vardelean/Hex-Preamp/GI13_Hex_Preamp/3D/GI13_RevA.jpg

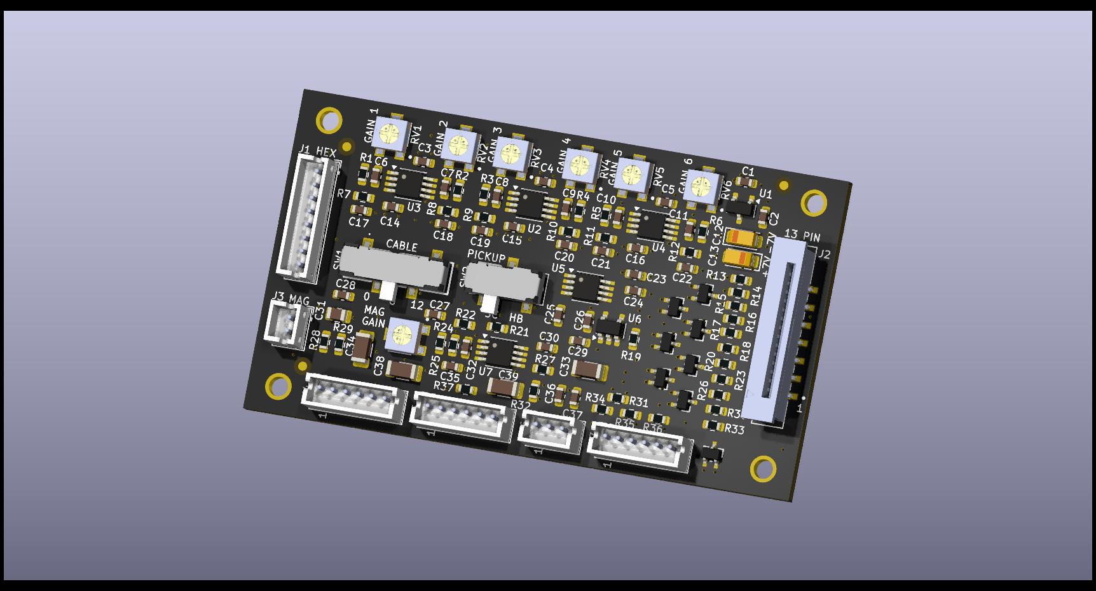
GI13_Hex_Preamp/3D/GI13_RevA.jpg
