vardelean/Hex-Preamp/Pics/GK_3_Finished_2.jpg

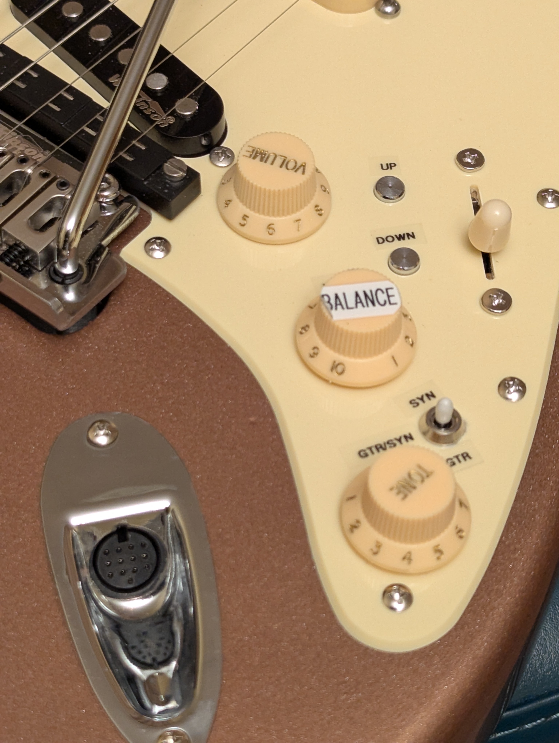
Pics/GK_3_Finished_2.jpg
