vardelean/Hex-Preamp/Pics/Hex_Preamp.jpg

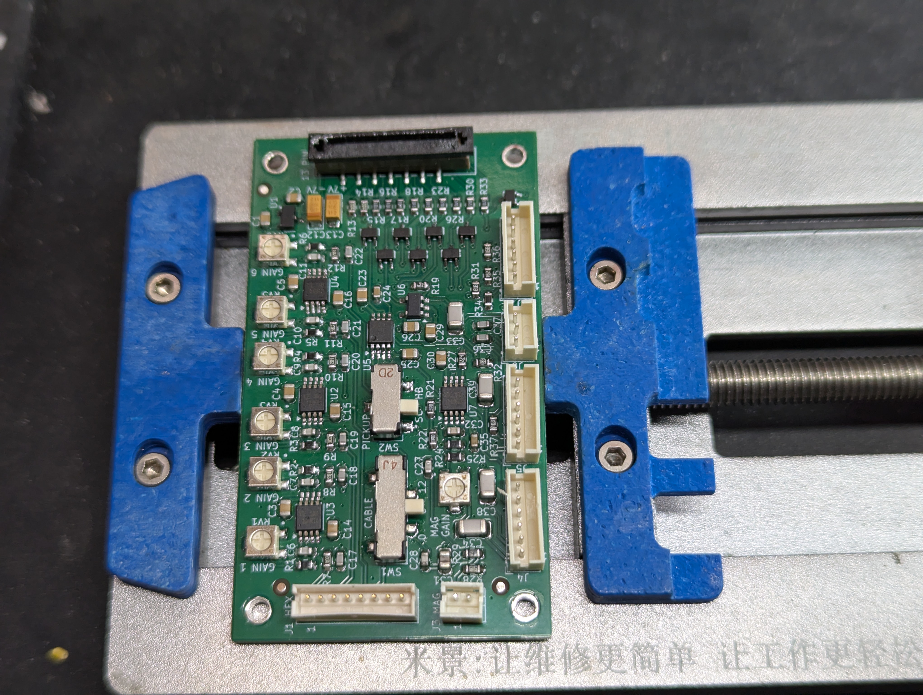
Pics/Hex_Preamp.jpg
